MythosMann/tg4x/2d-3d stuff/Artboard 1.png

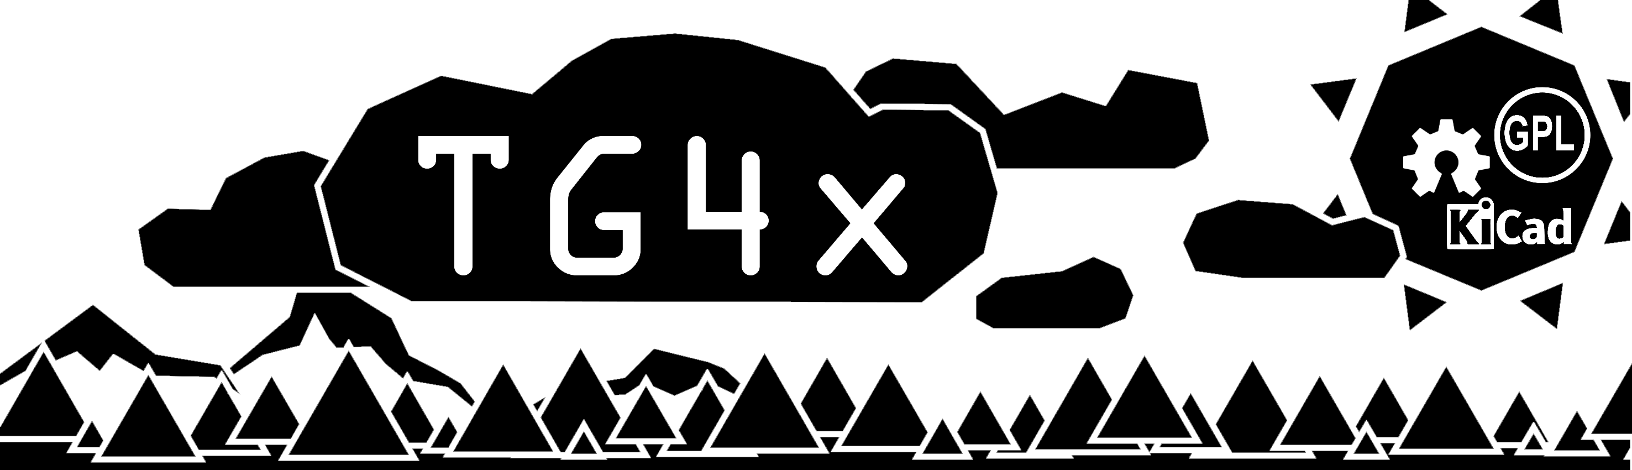
2d-3d stuff/Artboard 1.png
