MythosMann/tg4x/PCB_forest graphic.bmp

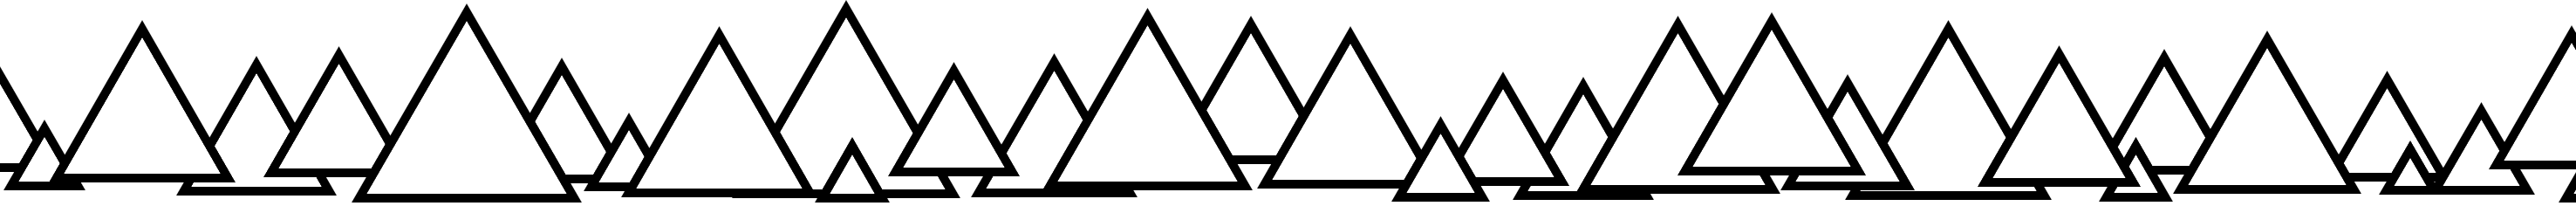
PCB_forest graphic.bmp
