MythosMann/tg4x/pcb_render_front.png

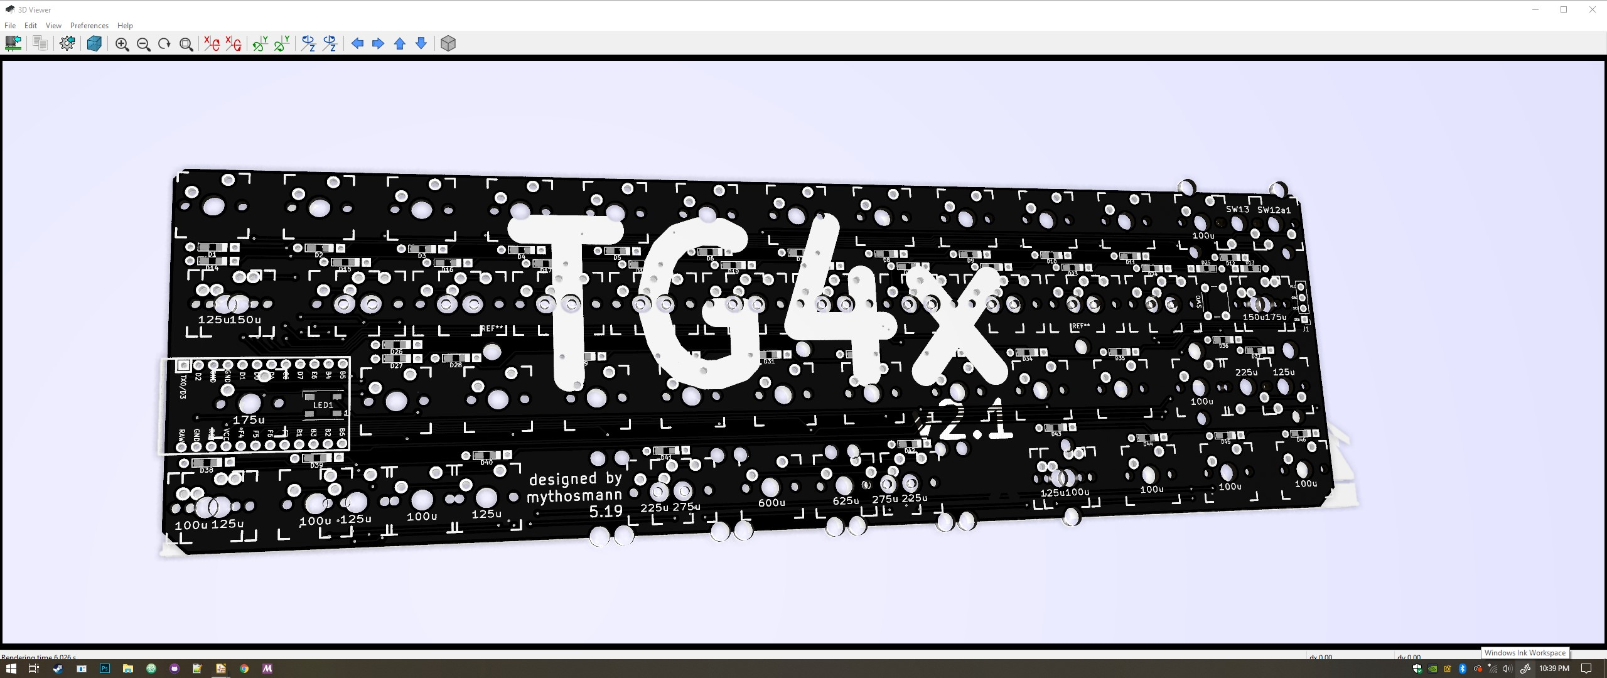
pcb_render_front.png
